digitalengineeringtech/fms_framework/test/fix_design/fmc_fix/sd.kicad_sch

## KiCad design test/fix_design/fmc_fix/sd.kicad_sch (2025-05-05)

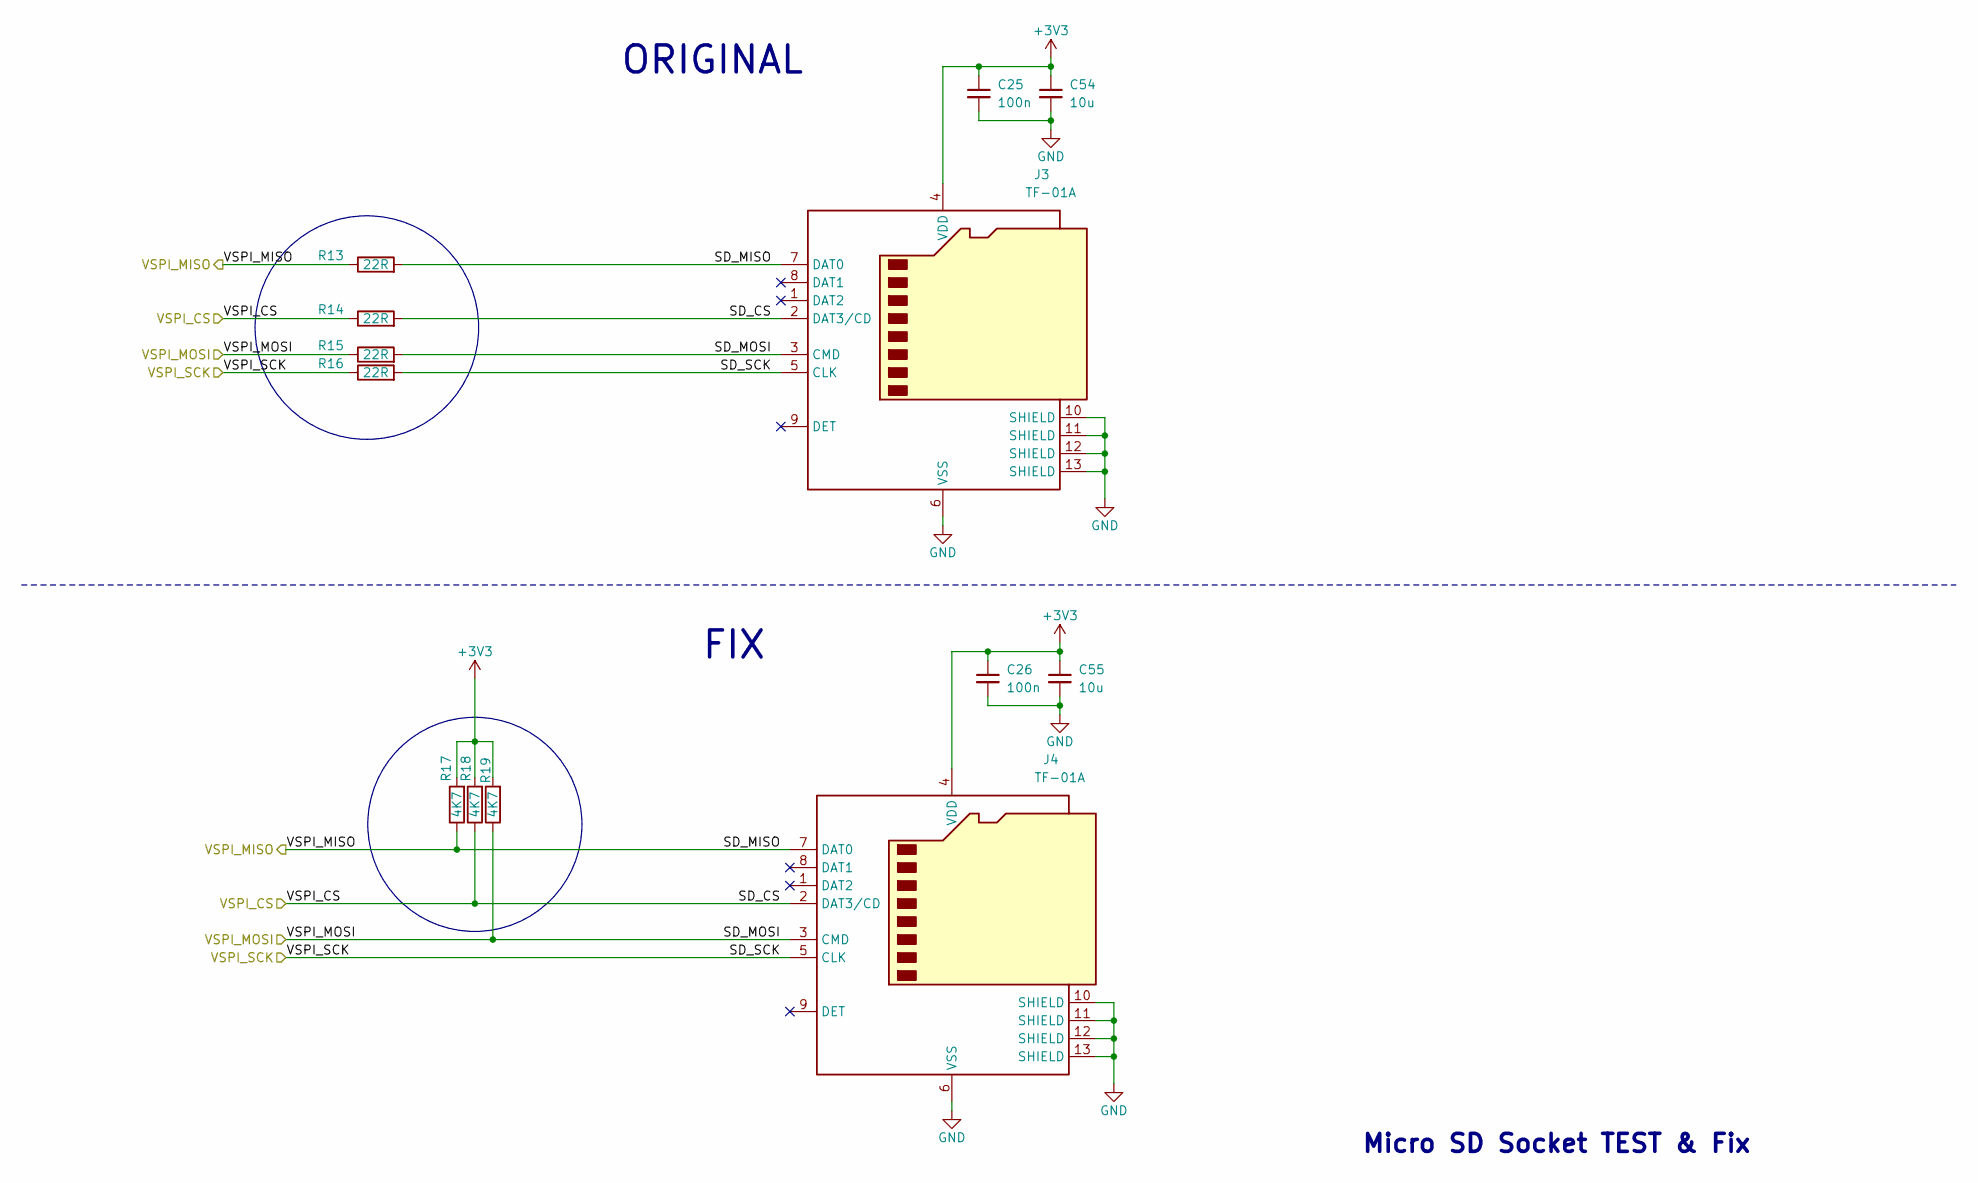
[picture p8: schematic sd.kicad_sch]

Parts:
C25, C26: 100n; C_0402_1005Metric; Manufacturer Part Number CC0402KRX7R9BB104; JLCPCB Part # C131394
C54, C55: 10u; C_0603_1608Metric; Manufacturer Part Number CC0603MRX5R8BB106; JLCPCB Part # C596327
J3, J4: TF-01A; TF-SMD_TF-01A; Manufacturer Part Number TF-01A; JLCPCB Part # C91145
R13, R14, R15, R16: 22R; R_0402_1005Metric; Manufacturer Part Number RC0402FR-0722RL; JLCPCB Part # C114765
R17, R18, R19: 4K7; R_0402_1005Metric; Manufacturer Part Number RC0402FR-0722RL; JLCPCB Part # C114765

Connections:
+3V3: C25.1, C26.1, C54.1, C55.1, J3.4 (VDD), J4.4 (VDD), R17.2, R18.2, R19.2
GND: C25.2, C26.2, C54.2, C55.2, J3.6 (VSS), J3.10 (SHIELD), J3.11 (SHIELD), J3.12 (SHIELD), J3.13 (SHIELD), J4.6 (VSS), J4.10 (SHIELD), J4.11 (SHIELD), J4.12 (SHIELD), J4.13 (SHIELD)
SD_CS: J3.2 (DAT3/CD), J4.2 (DAT3/CD), R14.1, R14.2, R18.1
SD_MISO: J3.7 (DAT0), J4.7 (DAT0), R13.1, R13.2, R17.1
SD_MOSI: J3.3 (CMD), J4.3 (CMD), R15.1, R15.2, R19.1
SD_SCK: J3.5 (CLK), J4.5 (CLK), R16.1, R16.2

Notes on the sheet:
Micro SD Socket TEST & Fix
FIX
ORIGINAL
