digitalengineeringtech/fms_framework/test/fix_design/fmc_fix/untitled.kicad_sch

## KiCad design test/fix_design/fmc_fix/untitled.kicad_sch (2025-05-05)

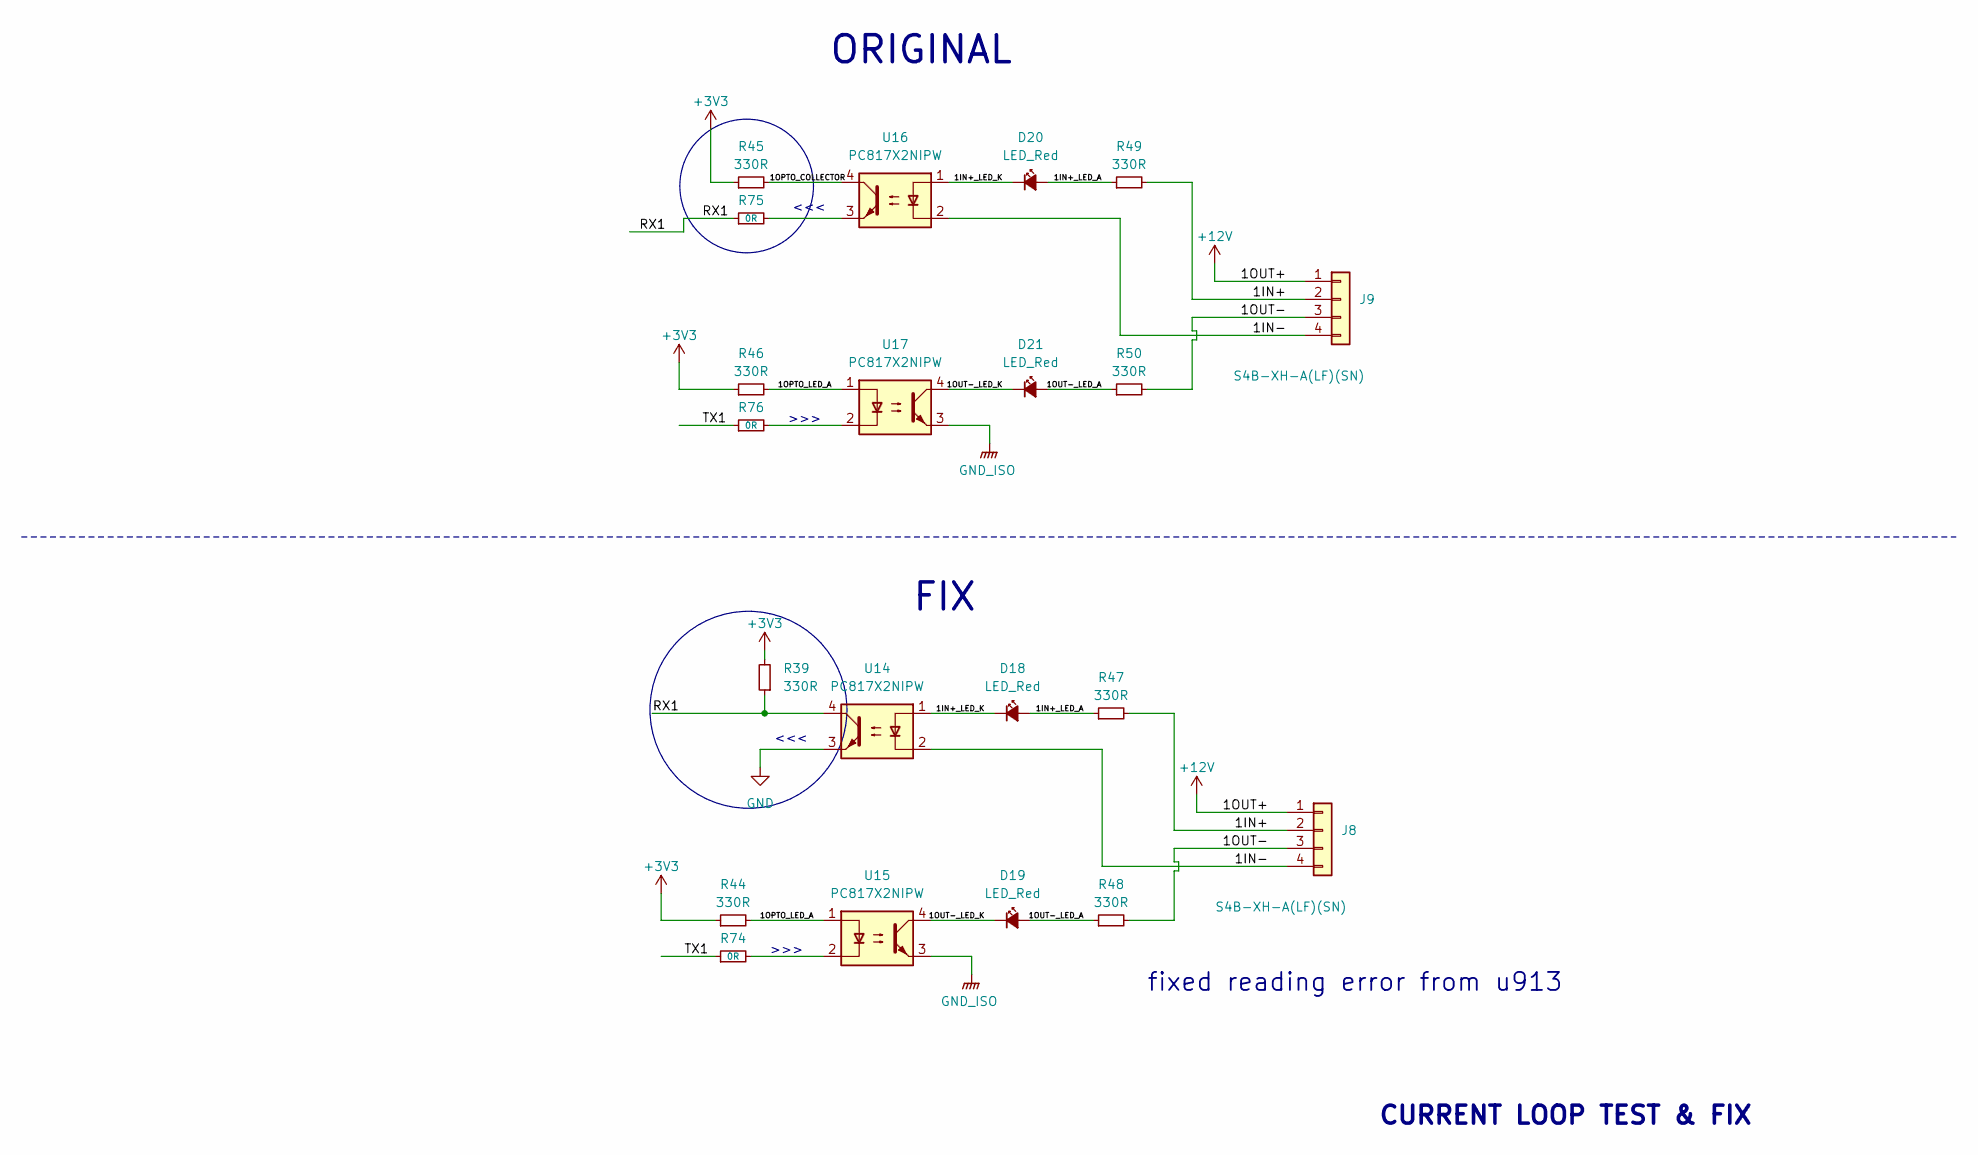
[picture p9: schematic untitled.kicad_sch]

Parts:
D18, D19, D20, D21: LED_Red; LED_0603_1608Metric; Manufacturer Part Number XL-1608SURC-06; JLCPCB Part # C965799
J8, J9: S4B-XH-A(LF)(SN); JST_XH_S4B-XH-A_1x04_P2.50mm_Horizontal; Manufacturer Part Number S4B-XH-A(LF)(SN); JLCPCB Part # C157925
R39, R44, R45, R46, R47, R48, R49, R50: 330R; R_0603_1608Metric; Manufacturer Part Number RC0603FR-07330RL; JLCPCB Part # C105881
R74, R75, R76: 0R; R_0402_1005Metric; Manufacturer Part Number RC0402FR-070RL; JLCPCB Part # C106231
U14, U15, U16, U17: PC817X2NIPW; SMDIP-4_W9.53mm; Manufacturer Part Number PC817X2NIPW; JLCPCB Part # C2840443

Connections:
1IN+: J8.2, J9.2, R47.2, R49.2
1IN+_LED_A: D18.2 (A), D20.2 (A), R47.1, R49.1
1IN+_LED_K: D18.1 (K), D20.1 (K), U14.1, U16.1
1IN-: J8.4, J9.4, U14.2, U16.2
1OPTO_COLLECTOR: R45.2, U16.4
1OPTO_LED_A: R44.2, R46.2, U15.1, U17.1
1OUT-: J8.3, J9.3, R48.2, R50.2
1OUT-_LED_A: D19.2 (A), D21.2 (A), R48.1, R50.1
1OUT-_LED_K: D19.1 (K), D21.1 (K), U15.4, U17.4
+3V3: R39.2, R44.1, R45.1, R46.1
+12V: J8.1, J9.1
GND: U14.3
GND_ISO: U15.3, U17.3
unnamed: R74.2, U15.2
unnamed: R75.2, U16.3
unnamed: R76.2, U17.2
RX1: R39.1, R75.1, U14.4
TX1: R74.1, R76.1

Notes on the sheet:
>>>
FIX
CURRENT LOOP TEST & FIX
fixed reading error from u913
<<<
ORIGINAL
