digitalengineeringtech/fms_framework/src/fms_main/src/_fms_touch.h

#ifndef _FMS_TOUCH_H
#define _FMS_TOUCH_H
#ifdef USE_TOUCH
#include <Arduino.h>
unsigned char Show_infor[6] = { 0x5A, 0xA5, 0x21, 0x82, 0x80, 0x00 };
unsigned char clean_infor[8] = { 0x5A, 0xA5, 0x5, 0x82, 0x80, 0x00, 0xff, 0xff };

// unsigned char Show_server_reply[21] = { 0x5A, 0xA5, 0x12, 0x82, 0x8F, 0x00, 0x53, 0x65, 0x72, 0x76, 0x65, 0x72, 0x2D, 0x32, 0x30, 0x30, 0x20, 0x4F, 0x4B, 0xff, 0xff };

unsigned char Show_server_Error[21] = { 0x5A, 0xA5, 0x12, 0x82, 0x8F, 0x00, 0x53, 0x65, 0x72, 0x76, 0x65, 0x72, 0x20, 0x45, 0x72, 0x72, 0x6F, 0x72, 0x21, 0xff, 0xff };
unsigned char Show_server_reply[6] = { 0x5A, 0xA5, 0x17, 0x82, 0x8F, 0x00 };
unsigned char Show_server_data[20] = { 0x46, 0x75, 0x65, 0x6C, 0x20, 0x46, 0x69, 0x6C, 0x6C, 0x69, 0x6E, 0x67, 0x20, 0x53, 0x74, 0x61, 0x74, 0x65, 0xff, 0xff };

unsigned char clean_infor_one[8] = { 0x5A, 0xA5, 0x5, 0x82, 0x8F, 0x00, 0xff, 0xff };

unsigned char Show_fuel[6] = { 0x5A, 0xA5, 0x17, 0x82, 0x00, 0x00 };  // Fuel type change
// unsigned char Default_Show_fuel[8] = { 0x5A, 0xA5, 0x06, 0x82, 0x00, 0x00, 0xff, 0xff };     // Fuel type change
unsigned char Show_dispenser_price[8] = { 0x5A, 0xA5, 0x05, 0x82, 0x11, 0x00, 0x00, 0x00 };  //dispenser price change
unsigned char Show_device_id[8] = { 0x5A, 0xA5, 0x05, 0x82, 0x14, 0x20, 0x00, 0x00 };        // device id change
unsigned char Show_Nozzle_NO[8] = { 0x5A, 0xA5, 0x05, 0x82, 0x14, 0x00, 0x00, 0x00 };        // Nozzle NO change

//for preset function liter and price default
unsigned char Default_preset_liter[10] = { 0x5A, 0xA5, 0x07, 0x82, 0x00, 0x11, 0x00, 0x00, 0x00, 0x00 };

//for preset function price default
unsigned char Default_preset_price[10] = { 0x5A, 0xA5, 0x07, 0x82, 0x00, 0x00, 0x00, 0x00, 0x00, 0x00 };

//for pin code
unsigned char Default_pin_code[10] = { 0x5A, 0xA5, 0x07, 0x82, 0x61, 0x00, 0x00, 0x00, 0x00, 0x00 };

//for preset function liter to show
unsigned char Show_F1_liter[10] = { 0x5A, 0xA5, 0x07, 0x82, 0x4A, 0x11, 0x00, 0x00, 0x00, 0x00 };
unsigned char Show_F2_liter[10] = { 0x5A, 0xA5, 0x07, 0x82, 0x4B, 0x11, 0x00, 0x00, 0x00, 0x00 };
unsigned char Show_F3_liter[10] = { 0x5A, 0xA5, 0x07, 0x82, 0x4C, 0x11, 0x00, 0x00, 0x00, 0x00 };
unsigned char Show_F4_liter[10] = { 0x5A, 0xA5, 0x07, 0x82, 0x4D, 0x11, 0x00, 0x00, 0x00, 0x00 };

//for preset function price to show
unsigned char Show_F1_price[10] = { 0x5A, 0xA5, 0x07, 0x82, 0x4A, 0x21, 0x00, 0x00, 0x00, 0x00 };
unsigned char Show_F2_price[10] = { 0x5A, 0xA5, 0x07, 0x82, 0x4B, 0x21, 0x00, 0x00, 0x00, 0x00 };
unsigned char Show_F3_price[10] = { 0x5A, 0xA5, 0x07, 0x82, 0x4C, 0x31, 0x00, 0x00, 0x00, 0x00 };
unsigned char Show_F4_price[10] = { 0x5A, 0xA5, 0x07, 0x82, 0x4D, 0x41, 0x00, 0x00, 0x00, 0x00 };

//page change setup
unsigned char Page_change[10] = { 0x5A, 0xA5, 0x07, 0x82, 0x00, 0x84, 0x5a, 0x01, 0x00, 0x00 };
unsigned char two_Page_change[10] = { 0x5A, 0xA5, 0x07, 0x82, 0x00, 0x84, 0x5a, 0x01, 0x00, 0x00 };
unsigned char four_Page_change[10] = { 0x5A, 0xA5, 0x07, 0x82, 0x00, 0x84, 0x5a, 0x01, 0x00, 0x01 };
unsigned char six_Page_change[10] = { 0x5A, 0xA5, 0x07, 0x82, 0x00, 0x84, 0x5a, 0x01, 0x00, 0x02 };
unsigned char eight_Page_change[10] = { 0x5A, 0xA5, 0x07, 0x82, 0x00, 0x84, 0x5a, 0x01, 0x00, 0x18 };

//for vehicle info default reset
unsigned char Show_car_no[15] = { 0x5A, 0xA5, 0x0C, 0x82, 0x23, 0x00, 0x43, 0x61, 0x72, 0x20, 0x4E, 0x6F, 0x2E, 0xff, 0xff };
unsigned char Show_member_id[17] = { 0x5A, 0xA5, 0x0E, 0x82, 0x24, 0x00, 0x4D, 0x65, 0x6D, 0x62, 0x65, 0x72, 0x20, 0x49, 0x44, 0xff, 0xff };
unsigned char Show_member_name[19] = { 0x5A, 0xA5, 0x10, 0x82, 0x25, 0x00, 0x4D, 0x65, 0x6D, 0x62, 0x65, 0x72, 0x20, 0x4E, 0x61, 0x6D, 0x65, 0xff, 0xff };
unsigned char Default_cash[8] = { 0x5A, 0xA5, 0x05, 0x82, 0x21, 0x00, 0x00, 0x00 };
unsigned char Default_vehicle[8] = { 0x5A, 0xA5, 0x05, 0x82, 0x22, 0x00, 0x00, 0x00 };

unsigned char Show_liter[10] = { 0x5A, 0xA5, 0x07, 0x82, 0x32, 0x00, 0x00, 0x00, 0x00, 0x00 };
unsigned char Show_price[10] = { 0x5A, 0xA5, 0x07, 0x82, 0x33, 0x00, 0x00, 0x00, 0x00, 0x00 };
unsigned char Show_default_liter[10] = { 0x5A, 0xA5, 0x07, 0x82, 0x32, 0x00, 0x00, 0x00, 0x00, 0x00 };
unsigned char Show_default_price[10] = { 0x5A, 0xA5, 0x07, 0x82, 0x33, 0x00, 0x00, 0x00, 0x00, 0x00 };

//screen off
unsigned char brightout[8] = { 0x5A, 0xA5, 0x05, 0x82, 0x00, 0x82, 0x01, 0x20 };
unsigned char brightin[8] = { 0x5A, 0xA5, 0x05, 0x82, 0x00, 0x82, 0x64, 0x20 };

unsigned char Clean_wifi_pass[8] = { 0x5A, 0xA5, 0x05, 0x82, 0x53, 0x00, 0xff, 0xff };
unsigned char Default_wifi_ssid[18] = { 0x5A, 0xA5, 0x0F, 0x82, 0x52, 0x00, 0x49, 0x6E, 0x70, 0x75, 0x74, 0x20, 0x53, 0x53, 0x49, 0x44, 0xff, 0xff };

//wifi icon
unsigned char Show_wifi_icon[8] = { 0x5A, 0xA5, 0x05, 0x82, 0x10, 0x02, 0x00, 0x00 };
unsigned char Hide_wifi_icon[8] = { 0x5A, 0xA5, 0x05, 0x82, 0x10, 0x02, 0x00, 0x01 };

//casher lock /unlock
unsigned char Show_casher_lock[8] = { 0x5A, 0xA5, 0x05, 0x82, 0x42, 0x00, 0x00, 0x00 };  // 0x05 is lock, 0x06 is unlock
// unsigned char Show_casher_unlock[8] = {0x5A, 0xA5, 0x05, 0x82, 0x42, 0x00, 0x00, 0x06};

unsigned char Show_icon_one[8] = { 0x5A, 0xA5, 0x05, 0x82, 0x10, 0x01, 0x00, 0x00 };
// unsigned char Hide_icon_one[8] = { 0x5A, 0xA5, 0x05, 0x82, 0x10, 0x01, 0x00, 0x01 };

unsigned char Show_icon_three[8] = { 0x5A, 0xA5, 0x05, 0x82, 0x10, 0x03, 0x00, 0x00 };
// unsigned char Hide_icon_three[8] = { 0x5A, 0xA5, 0x05, 0x82, 0x10, 0x03, 0x00, 0x01 };

unsigned char Show_cloud_icon[8] = { 0x5A, 0xA5, 0x05, 0x82, 0x10, 0x04, 0x00, 0x00 };
unsigned char Hide_cloud_icon[8] = { 0x5A, 0xA5, 0x05, 0x82, 0x10, 0x04, 0x00, 0x01 };

unsigned char Hide_dispenser_icon[8] = { 0x5A, 0xA5, 0x05, 0x82, 0x10, 0x11, 0x00, 0x01 };
unsigned char Show_dispenser_icon[8] = { 0x5A, 0xA5, 0x05, 0x82, 0x10, 0x11, 0x00, 0x00 };

// #################----for Hmi Two ---- ################################

//for preset function liter to show
unsigned char Show_F1_liter_two[10] = { 0x5A, 0xA5, 0x07, 0x82, 0x4A, 0x11, 0x00, 0x00, 0x00, 0x00 };
unsigned char Show_F2_liter_two[10] = { 0x5A, 0xA5, 0x07, 0x82, 0x4B, 0x11, 0x00, 0x00, 0x00, 0x00 };
unsigned char Show_F3_liter_two[10] = { 0x5A, 0xA5, 0x07, 0x82, 0x4C, 0x11, 0x00, 0x00, 0x00, 0x00 };
unsigned char Show_F4_liter_two[10] = { 0x5A, 0xA5, 0x07, 0x82, 0x4D, 0x11, 0x00, 0x00, 0x00, 0x00 };

//for preset function price to show
unsigned char Show_F1_price_two[10] = { 0x5A, 0xA5, 0x07, 0x82, 0x4A, 0x21, 0x00, 0x00, 0x00, 0x00 };
unsigned char Show_F2_price_two[10] = { 0x5A, 0xA5, 0x07, 0x82, 0x4B, 0x21, 0x00, 0x00, 0x00, 0x00 };
unsigned char Show_F3_price_two[10] = { 0x5A, 0xA5, 0x07, 0x82, 0x4C, 0x31, 0x00, 0x00, 0x00, 0x00 };
unsigned char Show_F4_price_two[10] = { 0x5A, 0xA5, 0x07, 0x82, 0x4D, 0x41, 0x00, 0x00, 0x00, 0x00 };

#define buzzer_pin_two 13

#define EEPROM_I2C_ADDRESS 0x50
#define SDA_pin 21
#define SCL_pin 22

#define RST_PIN_two 25  //for rfid two
#define SDA_PIN_two 5

MFRC522 Hmi_mfrc522(SDA_PIN_two, RST_PIN_two);

const char* mqtt_server = "192.168.0.100";
const char* mqtt_username = "detpos";
const char* mqtt_password = "asdffdsa";
const int mqtt_port = 1883;

WiFiClient espClient;
PubSubClient client(espClient);


char pump_permit[25] = "detpos/device/permit/1";
char final_data[25] = "detpos/device/Final/1";
char pin_Code[25] = "detpos/hmi/pinCode/0";
char FuelType_topic[40] = "detpos/local_server/initial2/det/0A0000";


char Hmi_Buffer[40];
char Car_no_two[15];
char Member_id_two[15];
char Member_name_two[15];
char Liter_count_two[5];
char Price_count_two[5];
int vehicle_type_two[3];
int cash_type_two[3];
char PIN_code_two[5];

//for function preset for hmi two
char F1_liter_two[5];
char F1_price_two[8];
char F2_liter_two[5];
char F2_price_two[8];
char F3_liter_two[5];
char F3_price_two[8];
char F4_liter_two[5];
char F4_price_two[8];

int PIN_CODE_two = 0;

int combine_Liter_two;
int combine_price_two;

int vehicle_value_two;
int cash_value_two;
int common_dispenser_price_two;

int dispenser_ID_two;
int common_pump_Id_two;

int F1_liter_value_two;
int F2_liter_value_two;
int F3_liter_value_two;
int F4_liter_value_two;

int F1_price_value_two;
int F2_price_value_two;
int F3_price_value_two;
int F4_price_value_two;

int Preset_total_eep_check_two = 0;

int Preset_eep_total_price_two = 0;
int Preset_eep_total_liter_two = 0;

String accessToken_two;

String vehicle_name_two;
String cash_name_two;
String Nozzle_name_two;
String rfid_content_two;

bool liter_check_two = false;
bool price_check_two = false;
bool over_all_li_price_check_two = false;
bool preset_check_two = false;

bool F1_liter_check_two = false;
bool F1_price_check_two = false;
bool F2_liter_check_two = false;
bool F2_price_check_two = false;
bool F3_liter_check_two = false;
bool F3_price_check_two = false;
bool F4_liter_check_two = false;
bool F4_price_check_two = false;
bool Total_check_two = false;

bool rfid_auth_check_two = false;
bool rfid_check_two = false;
bool rfid_card_check_two = true;

///////////////// common variable ////////////////////

char SSID_buffer[40];
char PASS_buffer[40];
char pricechangeary[7];
char permitArry[7];
char finaldataArry[3];
char charArray[5];
char priceArray[5];
char pinCodeArry[5];

char* Fuel_Type_1;
char* Fuel_Type_2;
char* Fuel_Type_3;
char* Fuel_Type_4;
char* Fuel_Type_5;
char* Fuel_Type_6;
char* Fuel_Type_7;
char* Fuel_Type_8;


String master_rfid = "POS2024";  // master rfid card
char SSID_buffer_temp[15] = "POS_Server";
char PASS_buffer_temp[15] = "asdffdsa";

bool rfid_condition;
bool master_check;

int page_check = 0;
int eep_PIN_CODE = 0;

int pumpmqttnum;
int common_Fuel_type;

int devicenum = 0;
int nozzlenum = 0;

int pumpid1;
int pumpid2;
int pumpid3;
int pumpid4;
int pumpid5;
int pumpid6;
int pumpid7;
int pumpid8;

int dispenser_1_price = 0;
int dispenser_2_price = 0;
int dispenser_3_price = 0;
int dispenser_4_price = 0;
int dispenser_5_price = 0;
int dispenser_6_price = 0;
int dispenser_7_price = 0;
int dispenser_8_price = 0;

int F1_eep_liter_value = 0;
int F2_eep_liter_value = 0;
int F3_eep_liter_value = 0;
int F4_eep_liter_value = 0;

int F1_eep_price_value = 0;
int F2_eep_price_value = 0;
int F3_eep_price_value = 0;
int F4_eep_price_value = 0;

int wifi_try = 0;

int casher_lock_check = 0;

bool isconnected = false;
bool brightness_check = true;
bool cloud_icon_check = false;
bool route_protect = true;

unsigned long Hmi_time = 0;
#endif // USE_TOUCH
#endif // _FMS_TOUCH_H
